alexminator/SML/data/img/alexminator.jpg

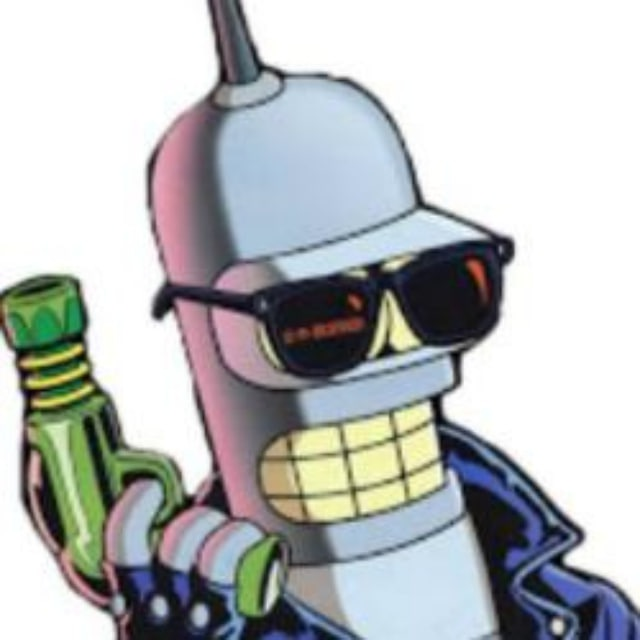
data/img/alexminator.jpg
