alexminator/SML/img/power lamp.png

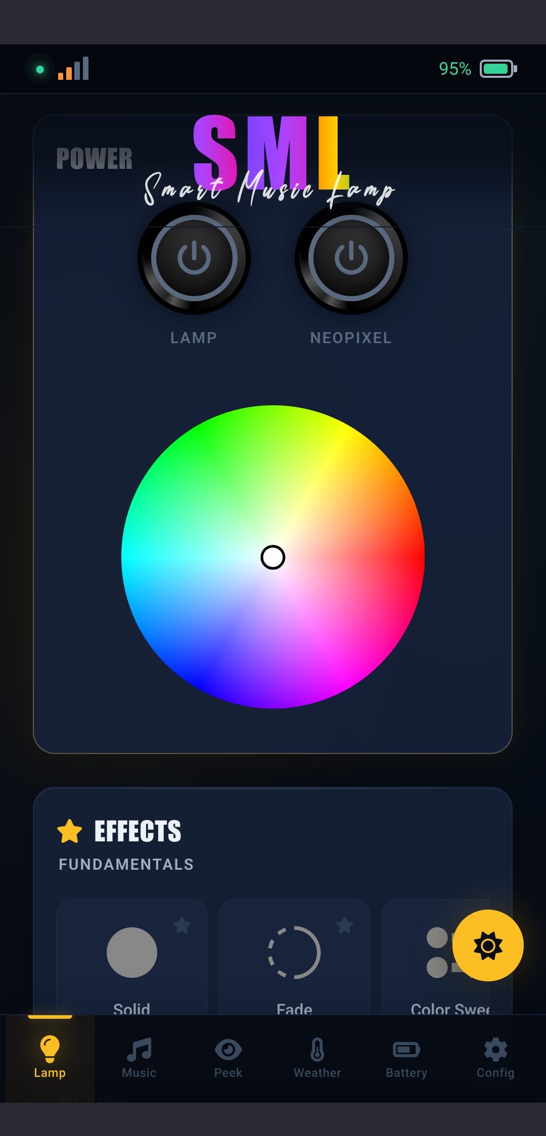
img/power lamp.png
