alexminator/SML/src/effects/EffectRegistry.cpp

// ──────────────────────────────────────────────────────────────────────────────
// EffectRegistry.cpp — Single definition of effect table
// ──────────────────────────────────────────────────────────────────────────────
#include "../state/AppState.h"   // Must precede EffectRegistry.h (needs StripLed)
#include "EffectRegistry.h"
#include "../config/debug_config.h"

#include <LittleFS.h>
#include <ArduinoJson.h>

// Effect headers (all subclass Effect)
#include "Fire.h"
#include "MovingDot.h"
#include "RainbowBeat.h"
#include "RedWhiteBlue.h"
#include "Ripple.h"
#include "Balls.h"
#include "Juggle.h"
#include "Sinelon.h"
#include "Comet.h"
#include "Breath.h"
#include "ColorSweep.h"

// ── Nuevos efectos WLED ──
#include "ColorWipe.h"
#include "TheaterChase.h"
#include "RunningLights.h"
#include "Dissolve.h"
#include "DualScan.h"
#include "Fade.h"
#include "Meteor.h"
#include "Sparkle.h"
#include "BPM.h"
#include "Plasma.h"
#include "Fireworks.h"
#include "Lightning.h"
#include "Pride2015.h"
#include "Colorwaves.h"
#include "Pacifica.h"
#include "TwinkleFOX.h"
#include "Aurora.h"
#include "Popcorn.h"

// ── Nuevos efectos prioritarios ─────────────────────────────────────────────
#include "LarsonScanner.h"
#include "Heartbeat.h"
#include "ICU.h"
#include "Sunrise.h"
#include "Drip.h"
#include "Candle.h"
#include "Chunchun.h"
#include "HalloweenEyes.h"

#include "Temp.h"
#include "Battery.h"
#include "../vu/vu1.h"
#include "../vu/vu2.h"
#include "../vu/vu3.h"
#include "../vu/vu4.h"
#include "../vu/vu5.h"
#include "../vu/vu6.h"
#include "../vu/vu8.h"
#include "../vu/vu9.h"

// ── Placeholder de efectos VU retirados (Gravimeter, PS1DGEQ, Palette Blend) ──
// DECISIÓN (Fase 5.1): se MANTIENEN las entradas en el registry aunque el efecto
// ya no exista. Motivo: el effectId es un índice, así que borrarlas desplazaría
// todos los efectos siguientes y invalidaría el `effectId` persistido en
// /state.json y el mapeo de IDs del frontend (data/js/websocket.js).
// La UI no ofrece estos IDs; si un cliente crudo los pide, la tira debe quedar
// APAGADA. Ojo: un render() totalmente vacío dejaba la tira congelada con el
// último frame del efecto anterior, porque StripLed::update() ya no hace show()
// por su cuenta al cambiar de efecto (Fase 2).
class RemovedEffect : public Effect {
public:
    RemovedEffect(CRGB* l, uint16_t n) : Effect(l, n) {}
    void render() override {
        FastLED.clear();
        FastLED.show();
    }
};

// ============================================================================
// EFFECT REGISTRY — definición única (ODR-safe)
// ============================================================================
// El orden debe coincidir con effectMap del frontend (data/js/main.js)
// y con los IDs históricos del switch original.
// ============================================================================

const EffectEntry effectRegistry[] = {
    { "fireStatus",             new FireEffect(leds, N_PIXELS) },
    { "movingdotStatus",        new MovingDotEffect(leds, N_PIXELS) },
    { "rainbowbeatStatus",      new RainbowBeatEffect(leds, N_PIXELS) },
    { "rwbStatus",              new RedWhiteBlueEffect(leds, N_PIXELS) },
    { "rippleStatus",           new RippleEffect(leds, N_PIXELS) },
    { "ballsStatus",            new BallsEffect(leds, N_PIXELS) },
    { "juggleStatus",           new JuggleEffect(leds, N_PIXELS) },
    { "sinelonStatus",          new SinelonEffect(leds, N_PIXELS) },
    { "cometStatus",            new CometEffect(leds, N_PIXELS) },
    { "breathStatus",           new BreathEffect(leds, N_PIXELS) },
    { "colorSweepStatus",       new ColorSweepEffect(leds, N_PIXELS) },
    { "rainbowVUStatus",        new RainbowVUEffect(leds, N_PIXELS) },
    { "oldVUStatus",            new OldskoolVUEffect(leds, N_PIXELS) },
    { "rainbowHueVUStatus",     new RainbowHueVUEffect(leds, N_PIXELS) },
    { "rippleVUStatus",         new RippleVUEffect(leds, N_PIXELS) },
    { "threebarsVUStatus",      new ThreebarsVUEffect(leds, N_PIXELS) },
    { "oceanVUStatus",          new OceanVUEffect(leds, N_PIXELS) },
    { "tempNEOStatus",          new TemperatureEffect(leds, N_PIXELS) },
    { "battNEOStatus",          new ChargeEffect(leds, N_PIXELS) },

    // ── Nuevos efectos WLED (20-27) ────────────────────────────────────────
    { "colorWipeStatus",        new ColorWipeEffect(leds, N_PIXELS) },
    { "theaterChaseStatus",     new TheaterChaseEffect(leds, N_PIXELS) },
    { "runningLightsStatus",    new RunningLightsEffect(leds, N_PIXELS) },
    { "dissolveStatus",         new DissolveEffect(leds, N_PIXELS) },
    { "dualScanStatus",         new DualScanEffect(leds, N_PIXELS) },
    { "fadeStatus",             new FadeEffect(leds, N_PIXELS) },
    { "meteorStatus",           new MeteorEffect(leds, N_PIXELS) },
    { "sparkleStatus",          new SparkleEffect(leds, N_PIXELS) },
    // ── Nuevos efectos WLED (28-34) ────────────────────────────────────────
    { "bpmStatus",              new BPMEffect(leds, N_PIXELS) },
    { "plasmaStatus",           new PlasmaEffect(leds, N_PIXELS) },
    { "fireworksStatus",        new FireworksEffect(leds, N_PIXELS) },
    { "lightningStatus",        new LightningEffect(leds, N_PIXELS) },
    { "pride2015Status",        new Pride2015Effect(leds, N_PIXELS) },
    { "colorwavesStatus",       new ColorwavesEffect(leds, N_PIXELS) },
    { "pacificaStatus",         new PacificaEffect(leds, N_PIXELS) },

    // ── Nuevos efectos WLED (35-37) ─────────────────────────────────────────
    { "twinkleFOXStatus",       new TwinkleFOXEffect(leds, N_PIXELS) },
    { "auroraStatus",           new AuroraEffect(leds, N_PIXELS) },
    { "popcornStatus",          new PopcornEffect(leds, N_PIXELS) },

    // ── Nuevos efectos prioritarios (38-45) ─────────────────────────────────
    { "larsonScannerStatus",    new LarsonScannerEffect(leds, N_PIXELS) },
    { "heartbeatStatus",        new HeartbeatEffect(leds, N_PIXELS) },
    { "icuStatus",              new ICUEffect(leds, N_PIXELS) },
    { "sunriseStatus",          new SunriseEffect(leds, N_PIXELS) },
    { "dripStatus",             new DripEffect(leds, N_PIXELS) },
    { "candleStatus",           new CandleEffect(leds, N_PIXELS) },
    { "chunchunStatus",         new ChunchunEffect(leds, N_PIXELS) },
    { "halloweenEyesStatus",    new HalloweenEyesEffect(leds, N_PIXELS) },

    // ── Nuevos efectos VU (46-50) ───────────────────────────────────────────
    // Efectos VU removidos: se mantienen como compatibilidad del registry para
    // que los IDs históricos no se reusen accidentalmente. No se muestran en la UI.
    // Si en el futuro no se necesitan, eliminar también su referencia en el frontend.
    { "gravimeterVUStatus",     new RemovedEffect(leds, N_PIXELS) },
    { "noisemeterVUStatus",     new NoisemeterVUEffect(leds, N_PIXELS) },
    { "djlightVUStatus",        new DJLightVUEffect(leds, N_PIXELS) },
    { "ps1dgeqVUStatus",        new RemovedEffect(leds, N_PIXELS) },
    { "paletteBlendVUStatus",   new RemovedEffect(leds, N_PIXELS) },
};

constexpr uint8_t EFFECT_COUNT =
    sizeof(effectRegistry) / sizeof(effectRegistry[0]);

// ============================================================================
// PERSISTENCIA DE PARÁMETROS
// ============================================================================

static uint8_t  _paramsDirty[EFFECT_COUNT];   // 1 = params cambiados, sin persistir
static uint32_t _paramsLastWriteMs = 0;       // millis() del último write real
static const uint32_t PARAMS_MIN_WRITE_INTERVAL_MS = 1000;  // debounce entre writes

void saveEffectParams(uint8_t effectId) {
    // Los IDs del frontend/registry son 1-based; los flags internos son 0-based.
    if (effectId == 0 || effectId > EFFECT_COUNT) return;
    _paramsDirty[effectId - 1] = 1;
}

void saveEffectParamsFlush() {
    if (xSemaphoreTake(dataMutex, pdMS_TO_TICKS(100)) != pdTRUE) {
#ifdef DEBUG_SYSTEM
        debuglnW("saveEffectParamsFlush: could not acquire mutex");
#endif
        return;
    }

    // ¿Hay algo pendiente y ya pasó el debounce mínimo? Si no, soltar y salir.
    bool anyDirty = false;
    for (uint8_t i = 0; i < EFFECT_COUNT; i++) {
        if (_paramsDirty[i]) { anyDirty = true; break; }
    }
    const uint32_t now = millis();
    if (!anyDirty || (now - _paramsLastWriteMs) < PARAMS_MIN_WRITE_INTERVAL_MS) {
        xSemaphoreGive(dataMutex);
        return;
    }

    // Capacidad ajustada al contenido real: ~140 B por efecto (nombre + 9 campos
    // numéricos/bool). Para 50 efectos reserva ~8,5 KB (antes eran 12 KB fijos).
    DynamicJsonDocument doc((size_t)EFFECT_COUNT * 160 + 512);
    for (uint8_t i = 0; i < EFFECT_COUNT; i++) {
        Effect* fx = effectRegistry[i].instance;
        if (!fx) continue;
        const char* name = effectRegistry[i].jsonName;
        JsonObject e = doc[name].to<JsonObject>();
        e["speed"]     = fx->getSpeed();
        e["intensity"] = fx->getIntensity();
        e["custom1"]   = fx->getCustom1();
        e["custom2"]   = fx->getCustom2();
        e["custom3"]   = fx->getCustom3();
        e["check1"]    = fx->getCheck1();
        e["check2"]    = fx->getCheck2();
        e["check3"]    = fx->getCheck3();
        e["palette"]   = fx->getPaletteIndex();
    }
    File f = LittleFS.open("/params.json", "w");
    if (f) {
        serializeJson(doc, f);
        f.close();
        // Persistido: limpiar flags y anotar el timestamp. Se hace dentro del
        // mutex para no perder un cambio que llegue en paralelo desde el handler.
        for (uint8_t i = 0; i < EFFECT_COUNT; i++) _paramsDirty[i] = 0;
        _paramsLastWriteMs = now;
    }
    xSemaphoreGive(dataMutex);
}

void loadEffectParams() {
    if (!LittleFS.exists("/params.json")) return;
    File f = LittleFS.open("/params.json", "r");
    if (!f) return;
    // Capacidad derivada del tamaño real del archivo (patrón ya usado en
    // AppState.cpp::loadBatteryLog). Antes 12288 fijos para un JSON de ~7,2 KB.
    DynamicJsonDocument doc(f.size() + 256);
    DeserializationError err = deserializeJson(doc, f);
    if (err) {
        f.close();
        return;
    }
    for (uint8_t i = 0; i < EFFECT_COUNT; i++) {
        const char* name = effectRegistry[i].jsonName;
        if (doc[name].isNull()) continue;
        Effect* fx = effectRegistry[i].instance;
        if (!fx) continue;
        JsonObject e = doc[name];
        fx->setSpeed(e["speed"] | DEFAULT_SPEED);
        fx->setIntensity(e["intensity"] | DEFAULT_INTENSITY);
        fx->setCustom1(e["custom1"] | DEFAULT_C1);
        fx->setCustom2(e["custom2"] | DEFAULT_C2);
        fx->setCustom3(e["custom3"] | DEFAULT_C3);
        // ⚠ Usar isNull() en vez de containsKey (ArduinoJson 7) — el operador
        // `|` devuelve false si el JSON guardó 0/1 (int) en vez de bool nativo.
        if (!e["check1"].isNull()) fx->setCheck1(e["check1"].as<int>() != 0);
        if (!e["check2"].isNull()) fx->setCheck2(e["check2"].as<int>() != 0);
        if (!e["check3"].isNull()) fx->setCheck3(e["check3"].as<int>() != 0);
        if (!e["palette"].isNull()) fx->setPaletteIndex(e["palette"].as<uint8_t>());
    }
    f.close();
}
