alexminator/SML/src/vu/vu.h

// ──────────────────────────────────────────────────────────────────────────────
// vu.h — Include único de todos los efectos VU meter
// ──────────────────────────────────────────────────────────────────────────────
// Todos heredan VUEffect.
// ──────────────────────────────────────────────────────────────────────────────
#pragma once

#include "VUEffect.h"
#include "vu1.h"    // RainbowVUEffect
#include "vu2.h"    // OldskoolVUEffect
#include "vu3.h"    // RainbowHueVUEffect
#include "vu4.h"    // RippleVUEffect
#include "vu5.h"    // ThreebarsVUEffect
#include "vu6.h"    // OceanVUEffect
#include "vu8.h"    // NoisemeterVUEffect
#include "vu9.h"    // DJLightVUEffect
