alexminator/SML/src/effects/effects.h

// ──────────────────────────────────────────────────────────────────────────────
// effects.h — Include único de todos los efectos
// ──────────────────────────────────────────────────────────────────────────────
// Después de mover todos los .h a src/effects/, este archivo sirve como punto
// único de inclusión. Cualquier .cpp que necesite efectos solo incluye este.
// ──────────────────────────────────────────────────────────────────────────────
#pragma once

// ── Efectos visuales activos ────────────────────────────────────────────────
#include "Balls.h"
#include "Breath.h"
#include "ColorSweep.h"
#include "ColorWipe.h"
#include "Comet.h"
#include "Dissolve.h"
#include "DualScan.h"
#include "Fade.h"
#include "Fire.h"
#include "Juggle.h"
#include "Meteor.h"
#include "MovingDot.h"
#include "RainbowBeat.h"
#include "RedWhiteBlue.h"
#include "Ripple.h"
#include "RunningLights.h"
#include "Sinelon.h"
#include "Sparkle.h"
#include "TheaterChase.h"
#include "BPM.h"
#include "Plasma.h"
#include "Fireworks.h"
#include "Lightning.h"
#include "Pride2015.h"
#include "Colorwaves.h"
#include "Pacifica.h"
#include "TwinkleFOX.h"
#include "Aurora.h"
#include "Popcorn.h"

// ── Nuevos efectos WLED prioritarios ────────────────────────────────────────
#include "LarsonScanner.h"
#include "Heartbeat.h"
#include "ICU.h"
#include "Sunrise.h"
#include "Drip.h"
#include "Candle.h"
#include "Chunchun.h"
#include "HalloweenEyes.h"

// ── Efectos indicadores (visualizan sensores) ───────────────────────────────
#include "Battery.h"
#include "Temp.h"
