alexminator/SML/src/vu/vu8.h

#pragma once
#include "../effects/Effect.h"
#include "../state/AppState.h"
#include "VUEffect.h"

// ──────────────────────────────────────────────────────────────────────────────
// NoisemeterVU — Medidor de ruido estilizado (colores fijos)
// ──────────────────────────────────────────────────────────────────────────────
// VU meter clásico con colores fijos: verde (bajo), amarillo (medio),
// rojo (alto). Con pico (peak) flotante.
// ⚠ Colores SEMÁNTICOS — no usa paletas (fijo)
// Params:
//   speed     → tasa de decaimiento del pico
//   intensity → sensibilidad
// ──────────────────────────────────────────────────────────────────────────────

class NoisemeterVUEffect : public VUEffect {
public:
    static const char _meta[];

    NoisemeterVUEffect(CRGB* l, uint16_t n) : VUEffect(l, n) {
        setToDefaults(_meta);
    }

    const char* getMeta() const override { return _meta; }

    void render() override {
        uint16_t height = auxReading();
        height = constrain(height, 0, numLeds - 1);

        fill_solid(leds, numLeds, CRGB::Black);

        // Draw bars with FIXED color gradient: green → yellow → red
        uint8_t greenZone  = numLeds * 2 / 3;
        uint8_t yellowZone = numLeds * 5 / 6;

        for (uint16_t i = 0; i <= height; i++) {
            if (i < greenZone) {
                leds[i] = CHSV(96, 255, 255);    // green (fijo)
            } else if (i < yellowZone) {
                leds[i] = CHSV(32, 255, 255);    // yellow (fijo)
            } else {
                leds[i] = CHSV(0, 255, 255);     // red (fijo)
            }
        }

        // Peak dot with decay
        if (height > _peak) _peak = height;
        if (_peak > 0 && _peak < numLeds) {
            leds[_peak] = CRGB::White;
        }

        dropPeak();
        averageReadings();
        // Brillo: lo aplica StripLed::update() una vez por frame (única fuente de verdad).
        FastLED.show();
    }
};

const char NoisemeterVUEffect::_meta[] =
    "Noisemeter@Decay,Sensitivity;;;;sx=128,ix=128";
